makbit/MDB1986/ModBus_RS232/modbus/port_1986BE1T/port.h

/*
 * FreeModbus Libary: Milandr Port Cortex-M
 * CopyLeft (C) 2022
 *
 * This library is free software; you can redistribute it and/or modify it.
 *
 * File: $Id$
 */

#ifndef _PORT_H
#define _PORT_H

#include <assert.h>
#include <inttypes.h>

#define	INLINE                      inline
#define PR_BEGIN_EXTERN_C           extern "C" {
#define	PR_END_EXTERN_C             }

#define ENTER_CRITICAL_SECTION()   (__disable_irq())
#define EXIT_CRITICAL_SECTION()    (__enable_irq()) 

typedef uint8_t BOOL;

typedef unsigned char UCHAR;
typedef char CHAR;

typedef uint16_t USHORT;
typedef int16_t SHORT;

typedef uint32_t ULONG;
typedef int32_t LONG;

#ifndef TRUE
#define TRUE            1
#endif

#ifndef FALSE
#define FALSE           0
#endif

#ifndef MILANDR_PORT
#define MILANDR_PORT    TRUE
#endif

#endif
